CivicTechTO/tRacket-sensor/noisemeter-device/access-point.h

/// @file
/// @brief Captive portal implementation for device setup.
/* noisemeter-device - Firmware for CivicTechTO's Noisemeter Device
 * Copyright (C) 2024  Clyne Sullivan, Nick Barnard
 *
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
 * You should have received a copy of the GNU General Public License
 * along with this program.  If not, see <https://www.gnu.org/licenses/>.
 */
#ifndef ACCESS_POINT_H
#define ACCESS_POINT_H

#include <DNSServer.h>
#include <WebServer.h>

#include <optional>

/**
 * @brief Manages the WiFi access point, captive portal, and user setup form.
 *
 * The access point is used to provide the user with a way to configure and set
 * up their device. After the user connects to the network using the fixed SSID
 * and passkey, they will be redirected to a setup form via a captive portal.
 * The form collects the user's WiFi credentials and any other needed
 * information (e.g. email address for first-time setup), then allows the
 * firmware to store the submitted response and connect to the internet.
 *
 * At the moment, once the access point is started it cannot be exited. The
 * firmware needs to do a software reset after handling a form submission to
 * begin normal operation.
 */
class AccessPoint : public RequestHandler
{
    /** Hard-coded SSID for the access point. */
    static constexpr auto SSID = "tRacket_Setup";
    /** Hard-coded passkey for the access point. */
    static constexpr auto Passkey = "noise123";

public:
    /**
     * Submission handler receives WebServer for input data and returns an
     * error message on failure.
     */
    using SubmissionHandler = std::optional<const char *> (*)(String, String, String);

    /**
     * Starts the WiFi access point using the fixed credentials.
     * @param func Callback to handle user setup form submission.
     */
    AccessPoint(SubmissionHandler func);

    /**
     * Enters an infinite loop to handle the access point and web server.
     */
    void run();

    /** Determines which HTTP requests should be handled. */
    virtual bool canHandle(WebServer&, HTTPMethod, const String&) override;
    /** Handles requests by redirecting to the setup page. */
    virtual bool handle(WebServer&, HTTPMethod, const String&) override;

private:

    unsigned long timeout;
    /** DNS server object for captive portal redirection. */
    DNSServer dns;
    /** Web server object for running the setup form. */
    WebServer server;
    /** Callback for setup form completion. */
    SubmissionHandler onCredentialsReceived;

    // There variables are used for handling setup form completion.
    String ssid, psk, email, finishHtml;
    bool finishGood;
    bool complete;
    bool restarting;

    /** Hard-coded IP address for the ESP32 when hosting the access point. */
    static const IPAddress IP;
    /** Hard-coded netmask for access point configuration. */
    static const IPAddress Netmask;
    /** Provides HTML for an error page with the given message. */
    static String htmlFromMsg(const char *msg, const char *extra = nullptr);

    static void taskOnCredentialsReceived(void *param);
};

#endif // ACCESS_POINT_H
