CivicTechTO/tRacket-sensor/noisemeter-device/ota-update.cpp

/* noisemeter-device - Firmware for CivicTechTO's Noisemeter Device
 * Copyright (C) 2024  Clyne Sullivan
 *
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
 * You should have received a copy of the GNU General Public License
 * along with this program.  If not, see <https://www.gnu.org/licenses/>.
 */
#include "ota-update.h"

#include <array>
#include <cstdint>
#include <ArduinoJson.h>
#include <HTTPClient.h>
#include <Update.h>
#include <WiFiClientSecure.h>
#include <mbedtls/pk.h>
#include <mbedtls/md.h>
#include <mbedtls/private_access.h>

#include "board.h"

// Public key for OTA signature verification
const unsigned char cert_ota [] PROGMEM = R"CERT(
-----BEGIN PUBLIC KEY-----
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
STejf1pUQ7jnm6WdvwSBupkCAwEAAQ==
-----END PUBLIC KEY-----
)CERT";

static bool applyUpdate(WiFiClientSecure& client, int totalSize);

bool downloadOTAUpdate(String url, String rootCA)
{
    if (url.isEmpty())
        return false;

    WiFiClientSecure client;
    client.setCACert(rootCA.c_str());

    HTTPClient https;
    if (https.begin(client, url)) {
        const auto code = https.GET();

        if (code == HTTP_CODE_OK || code == HTTP_CODE_MOVED_PERMANENTLY) {
            return applyUpdate(client, https.getSize());
        } else {
            SERIAL.print("Bad HTTP response: ");
            SERIAL.println(code);
        }
    } else {
        SERIAL.println("Unable to connect.");
    }

    return false;
}

bool applyUpdate(WiFiClientSecure& client, int totalSize)
{
    static std::array<uint8_t, 512> buffer;
    static std::array<uint8_t, 512> signature;
    mbedtls_pk_context pk;
    mbedtls_md_context_t rsa;
    mbedtls_pk_init( &pk );

    if (mbedtls_pk_parse_public_key(&pk, cert_ota, sizeof(cert_ota)) != 0) {
        SERIAL.println("Parsing public key failed!");
        return false;
    }

    if (!mbedtls_pk_can_do(&pk, MBEDTLS_PK_RSA)) {
        SERIAL.println("Public key is not an rsa key!");
        return false;
    }

    auto mdinfo = mbedtls_md_info_from_type(MBEDTLS_MD_SHA256);
    mbedtls_md_init(&rsa);
    mbedtls_md_setup(&rsa, mdinfo, 0);
    mbedtls_md_starts(&rsa);


    if (totalSize <= 0) {
        //SERIAL.println("Warning: Unable to determine update size.");
        //totalSize = UPDATE_SIZE_UNKNOWN;
        SERIAL.println("Unknown update size, stop.");
        return false;
    }

    if (!Update.begin(totalSize)) {
        SERIAL.println("Failed to begin Update.");
        return false;
    }

    bool first = true;
    while (client.connected() && (totalSize > 0 || totalSize == UPDATE_SIZE_UNKNOWN)) {
        const auto size = client.available();

        if (size > 0) {
            const auto bytesToRead = std::min(static_cast<int>(buffer.size()), size);
            const auto bytesRead = client.read(buffer.data(), bytesToRead);

            if (first) {
                if (bytesRead != signature.size()) {
                    SERIAL.println("Failed to read signature!");
                    return false;
                }
                std::copy(buffer.cbegin(), buffer.cend(), signature.begin());
                first = false;
            } else {
                if (!Update.write(buffer.data(), bytesRead)) {
                    SERIAL.println("Failed to write Update.");
                    return false;
                }

                mbedtls_md_update(&rsa, buffer.data(), bytesRead);
            }

            if (totalSize > 0)
                totalSize -= bytesRead;
        } else {
            delay(1);
        }
    }

    if (totalSize == 0) {
        const auto mdsize = mbedtls_md_get_size(mdinfo);
        unsigned char hash[mdsize];
        mbedtls_md_finish(&rsa, hash);

        auto ret = mbedtls_pk_verify(&pk, MBEDTLS_MD_SHA256, hash, sizeof(hash),
            signature.data(), signature.size());
        mbedtls_md_free(&rsa);
        mbedtls_pk_free(&pk);

        if (ret == 0) {
            Update.end(true);
            return true;
        } else {
            // validation failed, overwrite the first few bytes so this partition won't boot!
            SERIAL.println("Signature validation failed!");
            //ESP.partitionEraseRange( partition, 0, ENCRYPTED_BLOCK_SIZE);
            Update.abort();
        }
    }

    return false;
}
