CivicTechTO/tRacket-sensor/noisemeter-device/access-point-html.hpp

extern const char *HTML_HEADER;
extern const char *HTML_CONTAINER;
extern const char *HTML_FOOTER;
extern const char *HTML_BODY_FORM_HEADER;
extern const char *HTML_BODY_FORM_FOOTER;
extern const char *HTML_BODY_FORM_MANUAL;
