CivicTechTO/tRacket-sensor/noisemeter-device/storage.cpp

/* noisemeter-device - Firmware for CivicTechTO's Noisemeter Device
 * Copyright (C) 2024  Clyne Sullivan, Nick Barnard
 *
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
 * You should have received a copy of the GNU General Public License
 * along with this program.  If not, see <https://www.gnu.org/licenses/>.
 */
#include "storage.h"

#include <Arduino.h>
#include <CRC32.h>

#include <array>

void Storage::begin(UUID key)
{
    secret.key = key;

    EEPROMClass::begin(addrOf(Entry::TotalSize));
    delay(2000);  // Ensure the eeprom peripheral has enough time to initialize.
}

bool Storage::valid() const noexcept
{
    const auto calc = calculateChecksum();
    const auto addr = _data + addrOf(Entry::Checksum);
    const auto stored = *reinterpret_cast<uint32_t *>(addr);
    return stored == calc;
}

bool Storage::canStore(String str) const noexcept
{
    return str.length() < StringSize;
}

void Storage::clear() noexcept
{
    for (auto i = 0u; i < addrOf(Entry::TotalSize); ++i)
        writeByte(i, 0xFF);

    set(Entry::Token, "\0");
    EEPROMClass::commit();
}

String Storage::get(Entry entry) const noexcept
{
    if (entry != Entry::Checksum) {
        std::array<char, StringSize> buf;
        secret.decrypt(_data + addrOf(entry), buf.data(), StringSize);
        return buf.data();
    } else {
        return {};
    }
}

void Storage::set(Entry entry, String str) noexcept
{
    if (entry != Entry::Checksum && canStore(str)) {
        secret.encrypt(str.c_str(), _data + addrOf(entry), StringSize);
    }
}

void Storage::commit() noexcept
{
    const auto csum = calculateChecksum();
    writeUInt(addrOf(Entry::Checksum), csum);
    EEPROMClass::commit();
}

#ifdef STORAGE_SHOW_CREDENTIALS
Storage::operator String() const noexcept
{
    return String() +
           "SSID \"" + get(Entry::SSID) +
           "\" Passkey \"" + get(Entry::Passkey) +
           '\"';
}
#endif

uint32_t Storage::calculateChecksum() const noexcept
{
    const auto addr = _data + sizeof(uint32_t);
    const auto size = addrOf(Entry::TotalSize) - sizeof(uint32_t);
    return CRC32::calculate(addr, size);
}
